equant/apple2idiot/examples/20-multiapp-arduino/iss-tracker/apple2/gfx/iss-apple2_hgr.png

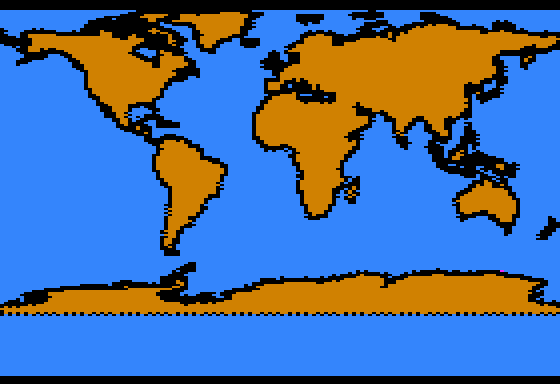
examples/20-multiapp-arduino/iss-tracker/apple2/gfx/iss-apple2_hgr.png
