equant/apple2idiot/card/silkscreen_manual.png

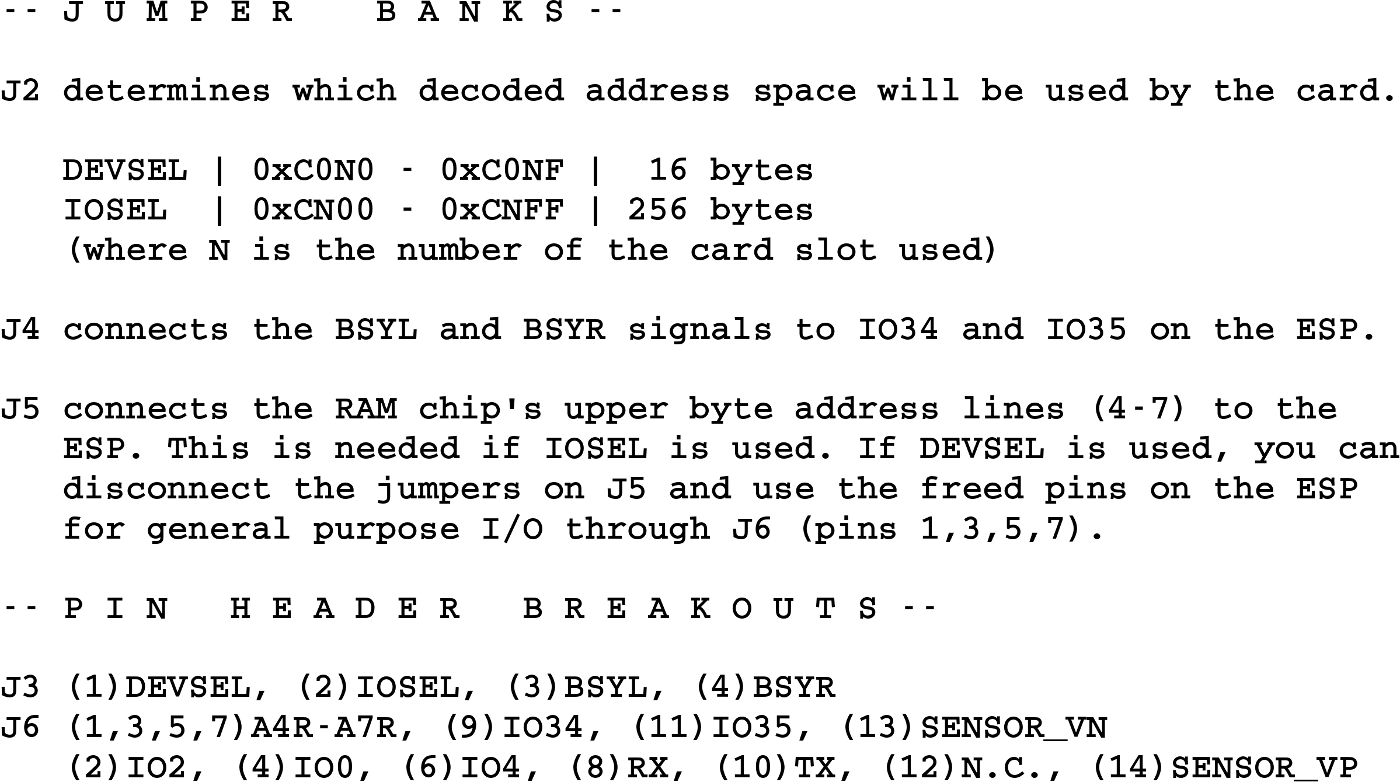
card/silkscreen_manual.png
