equant/apple2idiot/misc/media/ESP32_debug_output-reading_data.png

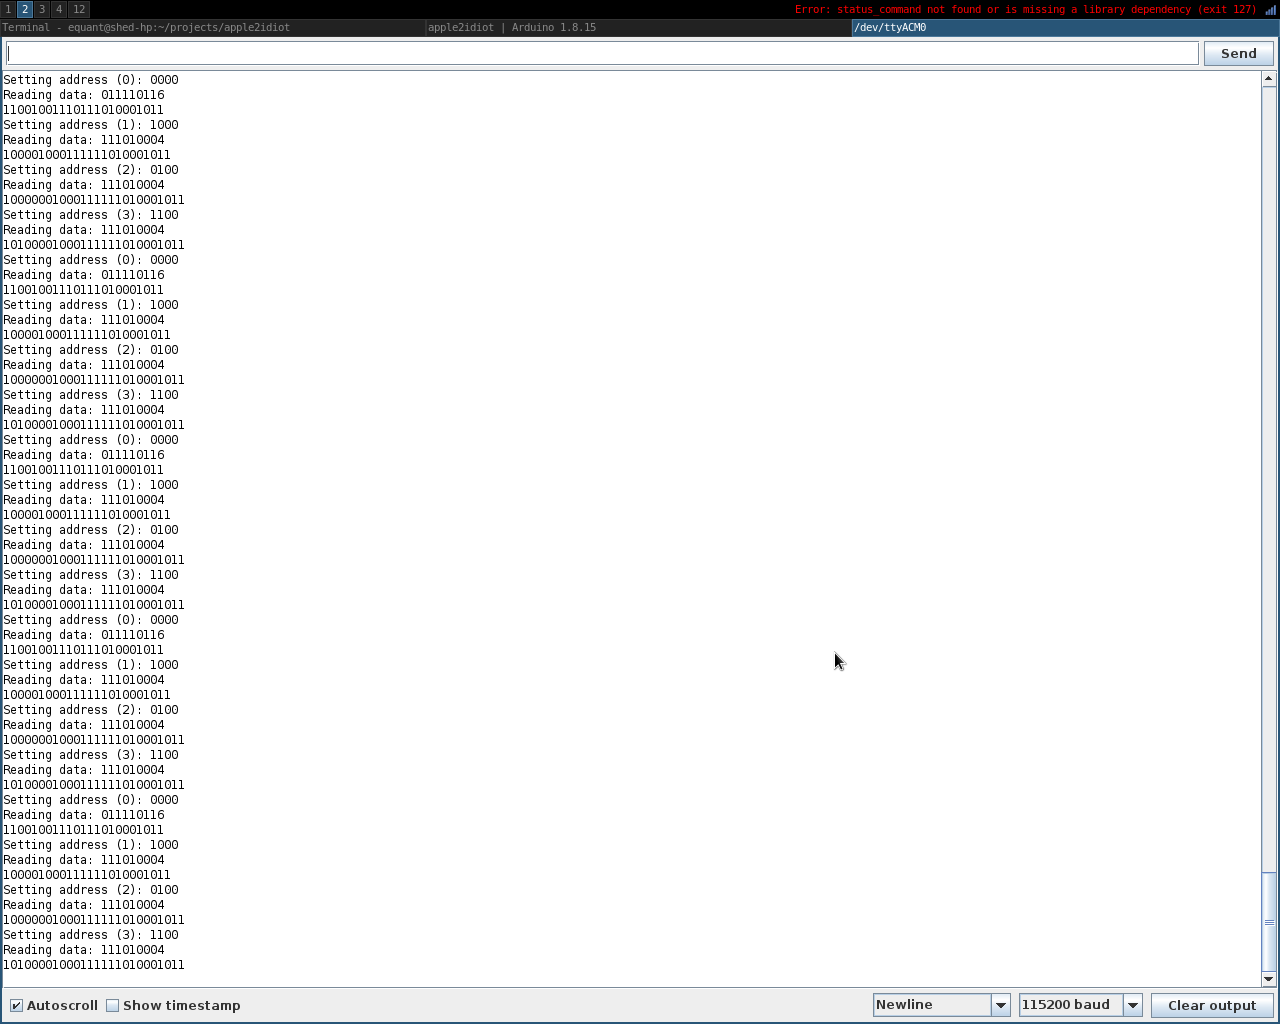
misc/media/ESP32_debug_output-reading_data.png
