equant/apple2idiot/examples/20-multiapp-arduino/iss-tracker/apple2/src/apple2.ip65/satellite.c

/**
 * ISS Tracker
 *
 * @author Thomas Cherryhomes
 * @email thom dot cherryhomes at gmail dot com
 * @license gpl v. 3, see LICENSE.md for details.
 */

#define CENTER_X 4
#define CENTER_Y 4

#include <apple2.h>
#include <tgi.h>
#include <stdint.h>
#include <stdbool.h>
#include <stdlib.h>
#include <string.h>
#include <conio.h>
#include <time.h>
#include <stdio.h>
#include "satellite.h"
#include "ip65.h"

const unsigned char _satellite[8] = {
  0x20, /* ..X.|.... */
  0x50, /* .X.X|.... */
  0xA4, /* X.X.|.X.. */
  0x58, /* .X.X|X... */
  0x1A, /* ...X|X.X. */
  0x05, /* ....|.X.X */
  0x0A, /* ....|X.X. */
  0x04, /* ....|.X.. */
};

// TODO: These tables are broken, recalculate them!

unsigned char xpos[360] = 
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
  unsigned char i,j;
  int8_t b;
  
  for (i=0;i<8;i++)
    {
      b=_satellite[i];
      for (j=0;j<16;j+=2)
	{
	  if (b < 0)
	    tgi_setcolor(TGI_COLOR_WHITE2);
	  else
	    tgi_setcolor(TGI_COLOR_BLACK2);
	  tgi_setpixel(x+j,y+i);
	  tgi_setpixel(x+j+1,y+i);
	  b <<= 1;
	}
    }
}
