equant/apple2idiot/examples/defunct-explorations/cc65-Chess-2/apple2-cc65/src/globals.h

/*
 *	globals.h
 *	cc65 Chess
 *
 *	Created by Stefan Wessels, February 2014.
 *
 */

#ifndef _GLOBALS_H_
#define _GLOBALS_H_

extern char		gChessBoard[8][8];
extern char		gCursorPos[2][2];
extern char     gTile[2];

extern char     state;

#endif //_GLOBALS_H_
